AJ6CU/benchduino-daughterboards/Arduino Nano/Examples/README.md

# Example for Arduino Nano Benchduino CPU Daughterboard

www.hamradioworkbench.com has designed and sells a general purpose development
board for Microcontrollers. They have provided the designs for both the CPU
Daughterboards as wells as the addon Prototype board.

This directory contains the code example (typically derived from the original 
Hamvention code of the published on the hamradioworkbench site)

There is absolutely no warranty here. Use this at your own risk!

Note that the Nano does not support Serial1, only Serial. Consequently, large portions
of the code related to CAT control had to be comment out. 

73
Mark Hatch
AJ6CU
