AJ6CU/benchduino-daughterboards/STM32/Gerbers/README.md

# STM32 "BluePill" CPU Daughterboard for Benchduino
 
www.hamradioworkbench.com has designed and sells a general purpose development
board for Microcontrollers. They have provided the designs for both the CPU
Daughterboards as wells as the addon Prototype board.

This directory contains a Zip file with the Gerbers for the CPU Daughterboards for a 
STM32 processor.

This design has been fabricated using these Gerbers and successfully runs the 
Hamvention demo program.

Once I receive these updated versions and have checked them out, i will update this
README file.

There is absolutely no warranty here. Use this at your own risk!

73
Mark Hatch
AJ6CU
