AJ6CU/benchduino-daughterboards/Arduino Nano/Documentation/BenchDuino Nano CPU BoardV1.png

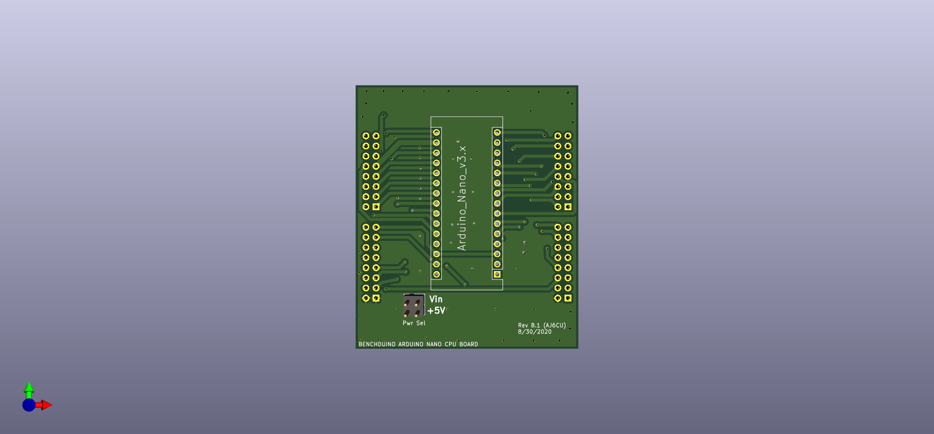
Arduino Nano/Documentation/BenchDuino Nano CPU BoardV1.png
